avm1234567/Customboot-32/CustomBoot-32/6. ESP_STM_FILE_CRC/Bootloader_C8TX/src/main.c

#include <libopencm3/stm32/gpio.h>
#include <libopencm3/stm32/rcc.h>
#include <libopencm3/stm32/usart.h>
#include <libopencm3/cm3/scb.h>
#include <libopencm3/cm3/systick.h>
#include <libopencm3/stm32/flash.h>
#include <libopencm3/cm3/cortex.h>
#include <libopencm3/stm32/crc.h>
#include <string.h>

#define DEFAULT_APP_ADDRESS (uint32_t)0x08000800
#define APP_ADDRESS (uint32_t)0x08000C00
uint32_t pinState;
uint8_t rx_buffer[1024];
#define CHUNK_SIZE 520
#define huart1 "STM"
uint32_t crc_STM;
uint32_t crc_ESP;
void uart_print_hex(uint32_t value);
void usart_setup(void);
void JumpToAddress(uint32_t addr);
void EraseUserApplication(uint32_t addr);
void WriteUserApplication(uint32_t addr, uint32_t *data, uint32_t dataSize, uint32_t offset);
void uart_transmit(uint32_t usart, const uint8_t *data, uint16_t len);
void uart_receive_blocking(uint32_t usart, uint8_t *buf, uint16_t len);
void ReceiveChunkOverUART(uint32_t addr, const char *str);
bool is_all_AA(const uint8_t *arr, size_t len);
uint32_t crc32_libopencm3_style(const uint8_t *data, size_t length);


bool is_all_AA(const uint8_t *arr, size_t len)
{
    for (size_t i = 0; i < len; i++)
    {
        if (arr[i] != 0xAA)
        {
            return false; // Found a mismatch
        }
    }
    return true; // All matched
}

uint32_t crc32_libopencm3_style(const uint8_t *data, size_t length)
{
    crc_reset();
    uint32_t word;
    for (size_t i = 0; i < length; i += 4)
    {
        word = ((uint32_t)data[i] << 24) |
               ((uint32_t)data[i + 1] << 16) |
               ((uint32_t)data[i + 2] << 8) |
               ((uint32_t)data[i + 3]);

        CRC_DR = word;
    }
    uint32_t crc_result = CRC_DR;
    return crc_result;
}

void usart_setup(void)
{

    rcc_periph_clock_enable(RCC_USART1);
    rcc_periph_clock_enable(RCC_GPIOA);
    gpio_set_mode(GPIOA, GPIO_MODE_OUTPUT_50_MHZ,
                  GPIO_CNF_OUTPUT_ALTFN_PUSHPULL, GPIO9);

    gpio_set_mode(GPIOA, GPIO_MODE_INPUT,
                  GPIO_CNF_INPUT_FLOAT, GPIO10);

    usart_set_baudrate(USART1, 115200);
    usart_set_databits(USART1, 8);
    usart_set_stopbits(USART1, USART_STOPBITS_1);
    usart_set_mode(USART1, USART_MODE_TX_RX);
    usart_set_parity(USART1, USART_PARITY_NONE);
    usart_set_flow_control(USART1, USART_FLOWCONTROL_NONE);
    usart_enable(USART1);
}

typedef void (*pFunction)(void);

void JumpToAddress(uint32_t addr)
{
    uint32_t jump_address = *(volatile uint32_t *)(addr + 4);

    /* Reset clocks to default reset state */
    RCC_APB2RSTR = 0xFFFFFFFF;
    RCC_APB2RSTR = 0x00000000;

    RCC_APB1RSTR = 0xFFFFFFFF;
    RCC_APB1RSTR = 0x00000000;

    RCC_APB2ENR = 0x00000000;
    RCC_APB1ENR = 0x00000000;
    RCC_AHBENR = 0x00000014;

    RCC_CFGR = 0x00000000;

    /* Disable interrupts */
    __asm__ volatile("CPSID I\n");
    /* Disable SysTick */
    STK_CSR &= ~STK_CSR_ENABLE;
    STK_CSR &= ~STK_CSR_TICKINT;
    STK_CVR = 0;
    SCB_VTOR = addr;
    __asm__ volatile("CPSIE I\n");
    __asm volatile(
        "msr msp, %[stack_ptr]  \n"
        "bx  %[reset_handler]   \n"
        :
        : [stack_ptr] "r"(*(volatile uint32_t *)addr),
          [reset_handler] "r"(jump_address)
        :);
}

void EraseUserApplication(uint32_t addr)
{

    flash_unlock();
    for (uint32_t i = 0; i < 8; i++)
    {
        flash_erase_page(addr + i * (uint32_t)1024);
    }
    flash_lock();
}

void WriteUserApplication(uint32_t addr, uint32_t *data, uint32_t dataSize, uint32_t offset)
{
    flash_unlock();
    for (uint32_t i = 0; i < dataSize; i++)
    {
        flash_program_word(addr + offset + (i * 4), data[i]);
    }
    flash_lock();
}

void uart_transmit(uint32_t usart, const uint8_t *data, uint16_t len)
{
    for (uint16_t i = 0; i < len; i++)
    {
        usart_send_blocking(usart, data[i]);
    }
}

void uart_receive_blocking(uint32_t usart, uint8_t *buf, uint16_t len)
{
    for (uint16_t i = 0; i < len; i++)
    {
        buf[i] = usart_recv_blocking(usart);
    }
}

void ReceiveChunkOverUART(uint32_t addr, const char *str)
{

    EraseUserApplication(addr);
    uint32_t offset = 0;
    uart_transmit(USART1, str, 8);
    // WriteUserApplication((uint32_t)addr, (uint32_t *)&rx_buffer[3], 128, offset);
    while (1)
    {
        // memset(rx_buffer, 0, CHUNK_SIZE);

        uart_receive_blocking(USART1, rx_buffer, CHUNK_SIZE);

        if (is_all_AA(rx_buffer, 520))
        {
            JumpToAddress((uint32_t)DEFAULT_APP_ADDRESS);
        }

        if (rx_buffer[CHUNK_SIZE - 1] == 0xAF)
        {
            crc_STM = 0x00;
            crc_ESP = 0x00;
            crc_STM = crc32_libopencm3_style(&rx_buffer[3], 512);
            crc_ESP = ((uint8_t)rx_buffer[515] << 24) |
                      ((uint8_t)rx_buffer[516] << 16) |
                      ((uint8_t)rx_buffer[517] << 8) |
                      ((uint8_t)rx_buffer[518]);

            if (crc_STM == crc_ESP)
            {
                WriteUserApplication((uint32_t)addr, (uint32_t *)&rx_buffer[3], 128, offset);

                JumpToAddress((uint32_t)addr);
            }
        }
        else if (rx_buffer[CHUNK_SIZE - 1] == 0x00)
        {
            crc_STM = 0x00;
            crc_ESP = 0x00;
            crc_STM = crc32_libopencm3_style(&rx_buffer[3], 512);
            crc_ESP = ((uint8_t)rx_buffer[515] << 24) |
                      ((uint8_t)rx_buffer[516] << 16) |
                      ((uint8_t)rx_buffer[517] << 8) |
                      ((uint8_t)rx_buffer[518]);

            if (crc_STM == crc_ESP)
            {
                WriteUserApplication((uint32_t)addr, (uint32_t *)&rx_buffer[3], 128, offset);

                offset += 512;

               
                    uart_print_hex(crc_STM);
            }
        }
    }
}

void uart_print_hex(uint32_t value) {
    const char hex[] = "0123456789abcdef";
    char buf[] = "crc matched: 0x00000000\r";
    for (int i = 22; i >= 15; i--) {
        buf[i] = hex[value & 0xF];
        value >>= 4;
    }
    uart_transmit(USART1, (uint8_t*)buf, sizeof(buf) - 1);
}


int main(void)
{
    rcc_clock_setup_pll(&rcc_hse_configs[RCC_CLOCK_HSE8_72MHZ]);
    rcc_periph_clock_enable(RCC_GPIOC);
    rcc_periph_clock_enable(RCC_GPIOB);

    gpio_set_mode(GPIOC, GPIO_MODE_OUTPUT_2_MHZ, GPIO_CNF_OUTPUT_PUSHPULL, GPIO13);
    gpio_set_mode(GPIOA, GPIO_MODE_INPUT, GPIO_CNF_INPUT_FLOAT, GPIO0);
    rcc_periph_clock_enable(RCC_CRC);

    usart_setup();
    for (int i = 0; i < 5; i++)
    {
        gpio_clear(GPIOC, GPIO13); // LED ON
        for (int i = 0; i < 800000; i++)
            __asm__("nop");
        gpio_set(GPIOC, GPIO13); // LED OFF
        for (int i = 0; i < 800000; i++)
            __asm__("nop");
    }
    while (1)
    {
        pinState = gpio_get(GPIOA, GPIO0);
        if (pinState == 0)
        {
            ReceiveChunkOverUART(APP_ADDRESS, "Send_A\r");
        }
        else
        {
            ReceiveChunkOverUART(APP_ADDRESS, "Send_B\r");
        }
    }
}
